dantudose/ESP32-Sparrow-rev3/software/zephyr/sparrow_test/src/cfb_font_0508.c

#include <stdint.h>
#include <zephyr/display/cfb.h>

#define FONT_FIRST_CHAR 32
#define FONT_LAST_CHAR 90
#define FONT_GLYPH_COUNT (FONT_LAST_CHAR - FONT_FIRST_CHAR + 1)
#define FONT_IDX(c) ((c) - FONT_FIRST_CHAR)

static const uint8_t cfb_font_0508[FONT_GLYPH_COUNT][5] = {
	[FONT_IDX(' ')] = { 0x00, 0x00, 0x00, 0x00, 0x00 },
	[FONT_IDX('!')] = { 0x00, 0x00, 0x5F, 0x00, 0x00 },
	[FONT_IDX('.')] = { 0x00, 0x60, 0x60, 0x00, 0x00 },
	[FONT_IDX(':')] = { 0x00, 0x36, 0x36, 0x00, 0x00 },
	[FONT_IDX('-')] = { 0x08, 0x08, 0x08, 0x08, 0x08 },

	[FONT_IDX('0')] = { 0x3E, 0x51, 0x49, 0x45, 0x3E },
	[FONT_IDX('1')] = { 0x00, 0x42, 0x7F, 0x40, 0x00 },
	[FONT_IDX('2')] = { 0x42, 0x61, 0x51, 0x49, 0x46 },
	[FONT_IDX('3')] = { 0x21, 0x41, 0x45, 0x4B, 0x31 },
	[FONT_IDX('4')] = { 0x18, 0x14, 0x12, 0x7F, 0x10 },
	[FONT_IDX('5')] = { 0x27, 0x45, 0x45, 0x45, 0x39 },
	[FONT_IDX('6')] = { 0x3C, 0x4A, 0x49, 0x49, 0x30 },
	[FONT_IDX('7')] = { 0x01, 0x71, 0x09, 0x05, 0x03 },
	[FONT_IDX('8')] = { 0x36, 0x49, 0x49, 0x49, 0x36 },
	[FONT_IDX('9')] = { 0x06, 0x49, 0x49, 0x29, 0x1E },

	[FONT_IDX('A')] = { 0x7E, 0x11, 0x11, 0x11, 0x7E },
	[FONT_IDX('B')] = { 0x7F, 0x49, 0x49, 0x49, 0x36 },
	[FONT_IDX('C')] = { 0x3E, 0x41, 0x41, 0x41, 0x22 },
	[FONT_IDX('D')] = { 0x7F, 0x41, 0x41, 0x22, 0x1C },
	[FONT_IDX('E')] = { 0x7F, 0x49, 0x49, 0x49, 0x41 },
	[FONT_IDX('F')] = { 0x7F, 0x09, 0x09, 0x09, 0x01 },
	[FONT_IDX('G')] = { 0x3E, 0x41, 0x49, 0x49, 0x7A },
	[FONT_IDX('H')] = { 0x7F, 0x08, 0x08, 0x08, 0x7F },
	[FONT_IDX('I')] = { 0x00, 0x41, 0x7F, 0x41, 0x00 },
	[FONT_IDX('J')] = { 0x20, 0x40, 0x41, 0x3F, 0x01 },
	[FONT_IDX('K')] = { 0x7F, 0x08, 0x14, 0x22, 0x41 },
	[FONT_IDX('L')] = { 0x7F, 0x40, 0x40, 0x40, 0x40 },
	[FONT_IDX('M')] = { 0x7F, 0x02, 0x0C, 0x02, 0x7F },
	[FONT_IDX('N')] = { 0x7F, 0x04, 0x08, 0x10, 0x7F },
	[FONT_IDX('O')] = { 0x3E, 0x41, 0x41, 0x41, 0x3E },
	[FONT_IDX('P')] = { 0x7F, 0x09, 0x09, 0x09, 0x06 },
	[FONT_IDX('Q')] = { 0x3E, 0x41, 0x51, 0x21, 0x5E },
	[FONT_IDX('R')] = { 0x7F, 0x09, 0x19, 0x29, 0x46 },
	[FONT_IDX('S')] = { 0x46, 0x49, 0x49, 0x49, 0x31 },
	[FONT_IDX('T')] = { 0x01, 0x01, 0x7F, 0x01, 0x01 },
	[FONT_IDX('U')] = { 0x3F, 0x40, 0x40, 0x40, 0x3F },
	[FONT_IDX('V')] = { 0x1F, 0x20, 0x40, 0x20, 0x1F },
	[FONT_IDX('W')] = { 0x7F, 0x20, 0x18, 0x20, 0x7F },
	[FONT_IDX('X')] = { 0x63, 0x14, 0x08, 0x14, 0x63 },
	[FONT_IDX('Y')] = { 0x03, 0x04, 0x78, 0x04, 0x03 },
	[FONT_IDX('Z')] = { 0x61, 0x51, 0x49, 0x45, 0x43 },
};

FONT_ENTRY_DEFINE(font0508,
		  5,
		  8,
		  CFB_FONT_MONO_VPACKED,
		  cfb_font_0508,
		  FONT_FIRST_CHAR,
		  FONT_LAST_CHAR);
